zoon81/nRF24l01_AVR_m88/drivers/inc/nRF24L01.h

/*
 * nRF24L01.h
 *
 *  Created on: Oct 15, 2017
 *      Author: t400
 */

#ifndef INC_NRF24L01_H_
#define INC_NRF24L01_H_


/* Memory Map */
#define CONFIG      0x00
#define EN_AA       0x01
#define EN_RXADDR   0x02
#define SETUP_AW    0x03
#define SETUP_RETR  0x04
#define RF_CH       0x05
#define RF_SETUP    0x06
#define STATUS      0x07
#define OBSERVE_TX  0x08
#define CD          0x09
#define RX_ADDR_P0  0x0A
#define RX_ADDR_P1  0x0B
#define RX_ADDR_P2  0x0C
#define RX_ADDR_P3  0x0D
#define RX_ADDR_P4  0x0E
#define RX_ADDR_P5  0x0F
#define TX_ADDR     0x10
#define RX_PW_P0    0x11
#define RX_PW_P1    0x12
#define RX_PW_P2    0x13
#define RX_PW_P3    0x14
#define RX_PW_P4    0x15
#define RX_PW_P5    0x16
#define FIFO_STATUS 0x17
#define DYNPD	    0x1C
#define FEATURE	    0x1D

/* Bit Mnemonics */
#define MASK_RX_DR  6
#define MASK_TX_DS  5
#define MASK_MAX_RT 4
#define EN_CRC      3
#define CRCO        2
#define PWR_UP      1
#define PRIM_RX     0
#define ENAA_P5     5
#define ENAA_P4     4
#define ENAA_P3     3
#define ENAA_P2     2
#define ENAA_P1     1
#define ENAA_P0     0
#define ERX_P5      5
#define ERX_P4      4
#define ERX_P3      3
#define ERX_P2      2
#define ERX_P1      1
#define ERX_P0      0
#define AW          0
#define ARD         4
#define ARC         0
#define PLL_LOCK    4
#define RF_DR       3
#define RF_PWR      6
#define RX_DR       6
#define TX_DS       5
#define MAX_RT      4
#define RX_P_NO     1
#define TX_FULL     0
#define PLOS_CNT    4
#define ARC_CNT     0
#define TX_REUSE    6
#define FIFO_FULL   5
#define TX_EMPTY    4
#define RX_FULL     1
#define RX_EMPTY    0
#define DPL_P5	    5
#define DPL_P4	    4
#define DPL_P3	    3
#define DPL_P2	    2
#define DPL_P1	    1
#define DPL_P0	    0
#define EN_DPL	    2
#define EN_ACK_PAY  1
#define EN_DYN_ACK  0

/* Instruction Mnemonics */
#define R_REGISTER    0x00
#define W_REGISTER    0x20
#define REGISTER_MASK 0x1F
#define ACTIVATE      0x50
#define R_RX_PL_WID   0x60
#define R_RX_PAYLOAD  0x61
#define W_TX_PAYLOAD  0xA0
#define W_ACK_PAYLOAD 0xA8
#define FLUSH_TX      0xE1
#define FLUSH_RX      0xE2
#define REUSE_TX_PL   0xE3
#define NOP           0xFF

struct payload;

void nRF2401_init(uint8_t NRF_CSN, uint8_t NRF_CE);
void nRF_2401_reg_write_m(uint8_t reg, uint8_t *value, uint8_t size, uint8_t CSN);
void nRF_2401_reg_write_s(uint8_t reg, uint8_t data, uint8_t CSN);
uint8_t nRF_2401_reg_read(uint8_t reg, uint8_t CSN);
void nRF2401_transmit_payload(struct payload *payload, uint8_t CSN, uint8_t NRF_CE);
void nRF2401_reset_IRQ(uint8_t CSN);
void nRF2401_set_receiver_mode(uint8_t CE);
void nRF2401_receive_payload(uint8_t CSN, uint8_t CE, struct payload *buffer);
void nRF2401_receive_payload_it(uint8_t CSN, uint8_t CE, struct payload *buffer);

#endif /* INC_NRF24L01_H_ */
