zoon81/nRF24l01_AVR_m88/HAL/adc.c

#include "adc.h"

void adc_init(){
    ADMUX |= BIT(REFS0) | BIT(ADLAR);
    ADCSRA |= BIT(ADEN) | BIT(ADPS2) | BIT(ADPS1) | BIT(ADPS0);
    DIDR0 = 0xFF;
}
uint8_t adc_read(uint8_t channel){
    ADMUX = (ADMUX & 0xF0) | channel;
    ADCSRA |= BIT(ADSC);
    while(!(ADCSRA & BIT(ADIF)));
    ADCSRA |= BIT(ADIF);
    return ADCH;
}
void adc_startconversion(uint8_t channel){
    ADMUX = (ADMUX & 0xF0) | channel;
    ADCSRA |= BIT(ADSC);
}
