zoon81/nRF24l01_AVR_m88/HAL/inc/spi.h

/*
 * spi.h
 *
 *  Created on: Oct 15, 2017
 *      Author: t400
 */

#ifndef INC_SPI_H_
#define INC_SPI_H_
#include "main.h"

#define DD_MOSI		DDB3
#define DD_SCK		DDB5

void spi_init(uint8_t CSN);
uint8_t spi_transfer(uint8_t data);

#endif /* INC_SPI_H_ */
